goldenjinjo/Bellerophon-PCB/bellerophon/component_libraries/3D_models/headers-2-54mm-1.snapshot.13/Header, Male, 2.54mm, 1x18.JPG

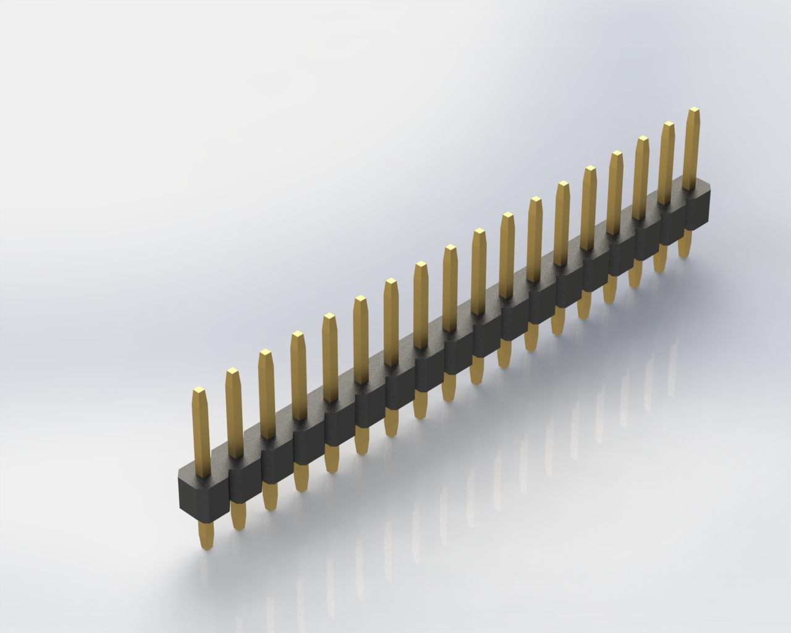
bellerophon/component_libraries/3D_models/headers-2-54mm-1.snapshot.13/Header, Male, 2.54mm, 1x18.JPG
