goldenjinjo/Bellerophon-PCB/bellerophon/component_libraries/3D_models/headers-2-54mm-1.snapshot.13/Header, Male, 2.54mm, 1x3.STEP

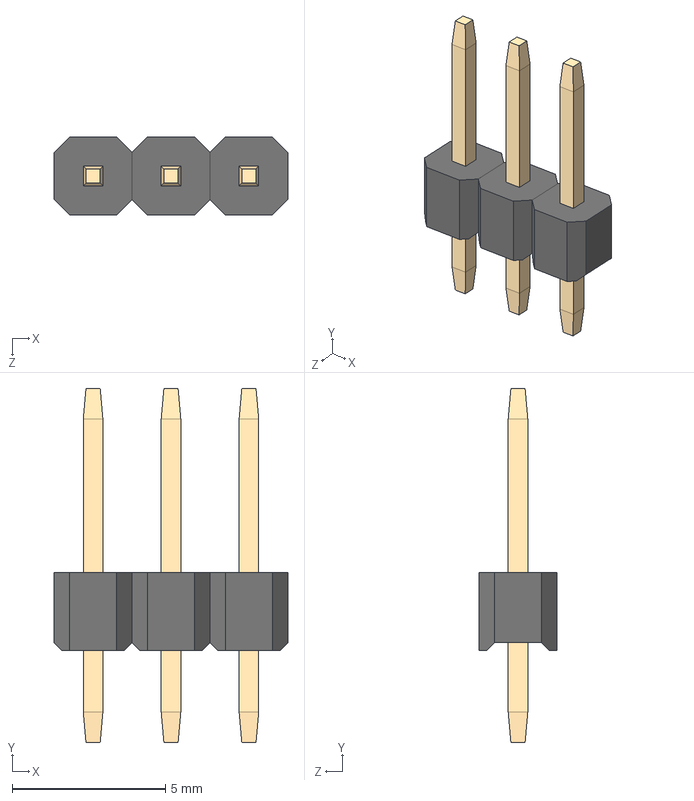
[picture p26: CAD file, 2024-06-30]
bellerophon/component_libraries/3D_models/headers-2-54mm-1.snapshot.13/Header, Male, 2.54mm, 1x3.STEP
7.62 x 11.5 x 2.54 mm
